aluiziotomazelli/smart-farm-water-tank/logger/raw-logs/field_test_logs_20260715_101221.txt

[2026-07-15 10:12:26.573] [192.168.1.64] I (2303673) UsSensor: 54.6-0, 54.3-0, 54.6-0, 54.7-0, 55.4-0, 54.5-0, 65.0-0
[2026-07-15 10:12:26.601] [192.168.1.64] I (2303693) WaterTankApp: Distance: 54.7 - UsResult 0 | Battery: 3810
[2026-07-15 10:12:32.692] [192.168.1.64] I (2309793) UsSensor: 55.1-0, 59.8-0, 54.5-0, 55.9-0, 64.0-0, 55.9-0, 54.7-0
[2026-07-15 10:12:32.729] [192.168.1.64] I (2309813) WaterTankApp: Distance: 55.2 - UsResult 0 | Battery: 3810
[2026-07-15 10:12:38.813] [192.168.1.64] I (2315913) UsSensor: 54.1-0, 56.1-0, 53.7-0, 54.2-0, 53.7-0, 53.7-0, 54.5-0
[2026-07-15 10:12:38.841] [192.168.1.64] I (2315933) WaterTankApp: Distance: 54.3 - UsResult 0 | Battery: 3810
[2026-07-15 10:12:44.934] [192.168.1.64] I (2322033) UsSensor: 55.1-0, 53.7-0, 54.5-0, 64.4-0, 53.4-0, 57.3-0, 53.7-0
[2026-07-15 10:12:44.963] [192.168.1.64] I (2322053) WaterTankApp: Distance: 54.6 - UsResult 0 | Battery: 3810
[2026-07-15 10:12:51.062] [192.168.1.64] I (2328153) UsSensor: 54.6-0, 65.4-0, 54.2-0, 54.5-0, 54.0-0, 54.0-0, 55.6-0
[2026-07-15 10:12:51.082] [192.168.1.64] I (2328173) WaterTankApp: Distance: 54.5 - UsResult 0 | Battery: 3810
[2026-07-15 10:12:57.176] [192.168.1.64] I (2334273) UsSensor: 54.6-0, 54.7-0, 54.2-0, 53.2-0, 54.0-0, 54.2-0, 63.4-0
[2026-07-15 10:12:57.203] [192.168.1.64] I (2334293) WaterTankApp: Distance: 54.2 - UsResult 0 | Battery: 3810
[2026-07-15 10:13:03.296] [192.168.1.64] I (2340393) UsSensor: 53.3-0, 53.4-0, 53.7-0, 54.2-0, 66.5-0, 57.9-0, 54.0-0
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
[2026-07-15 11:41:11.873] [192.168.1.64] I (7628993) UsSensor: 37.0-0, 39.0-0, 36.7-0, 37.1-0, 37.1-0, 37.0-0, 36.4-0
[2026-07-15 11:41:11.908] [192.168.1.64] I (7629013) WaterTankApp: Distance: 37.2 - UsResult 0 | Battery: 3806
[2026-07-15 11:41:17.993] [192.168.1.64] I (7635113) UsSensor: 36.0-0, 36.1-0, 37.1-0, 38.0-0, 36.7-0, 36.7-0, 37.1-0
[2026-07-15 11:41:18.021] [192.168.1.64] I (7635133) WaterTankApp: Distance: 36.8 - UsResult 0 | Battery: 3806
[2026-07-15 11:41:24.118] [192.168.1.64] I (7641233) UsSensor: 36.0-0, 36.1-0, 36.8-0, 37.1-0, 36.1-0, 36.1-0, 36.1-0
[2026-07-15 11:41:24.141] [192.168.1.64] I (7641253) WaterTankApp: Distance: 36.3 - UsResult 0 | Battery: 3806
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
