aluiziotomazelli/smart-farm-water-tank/docs/water-tank.kicad_sch

## KiCad design docs/water-tank.kicad_sch (2026-08-27)

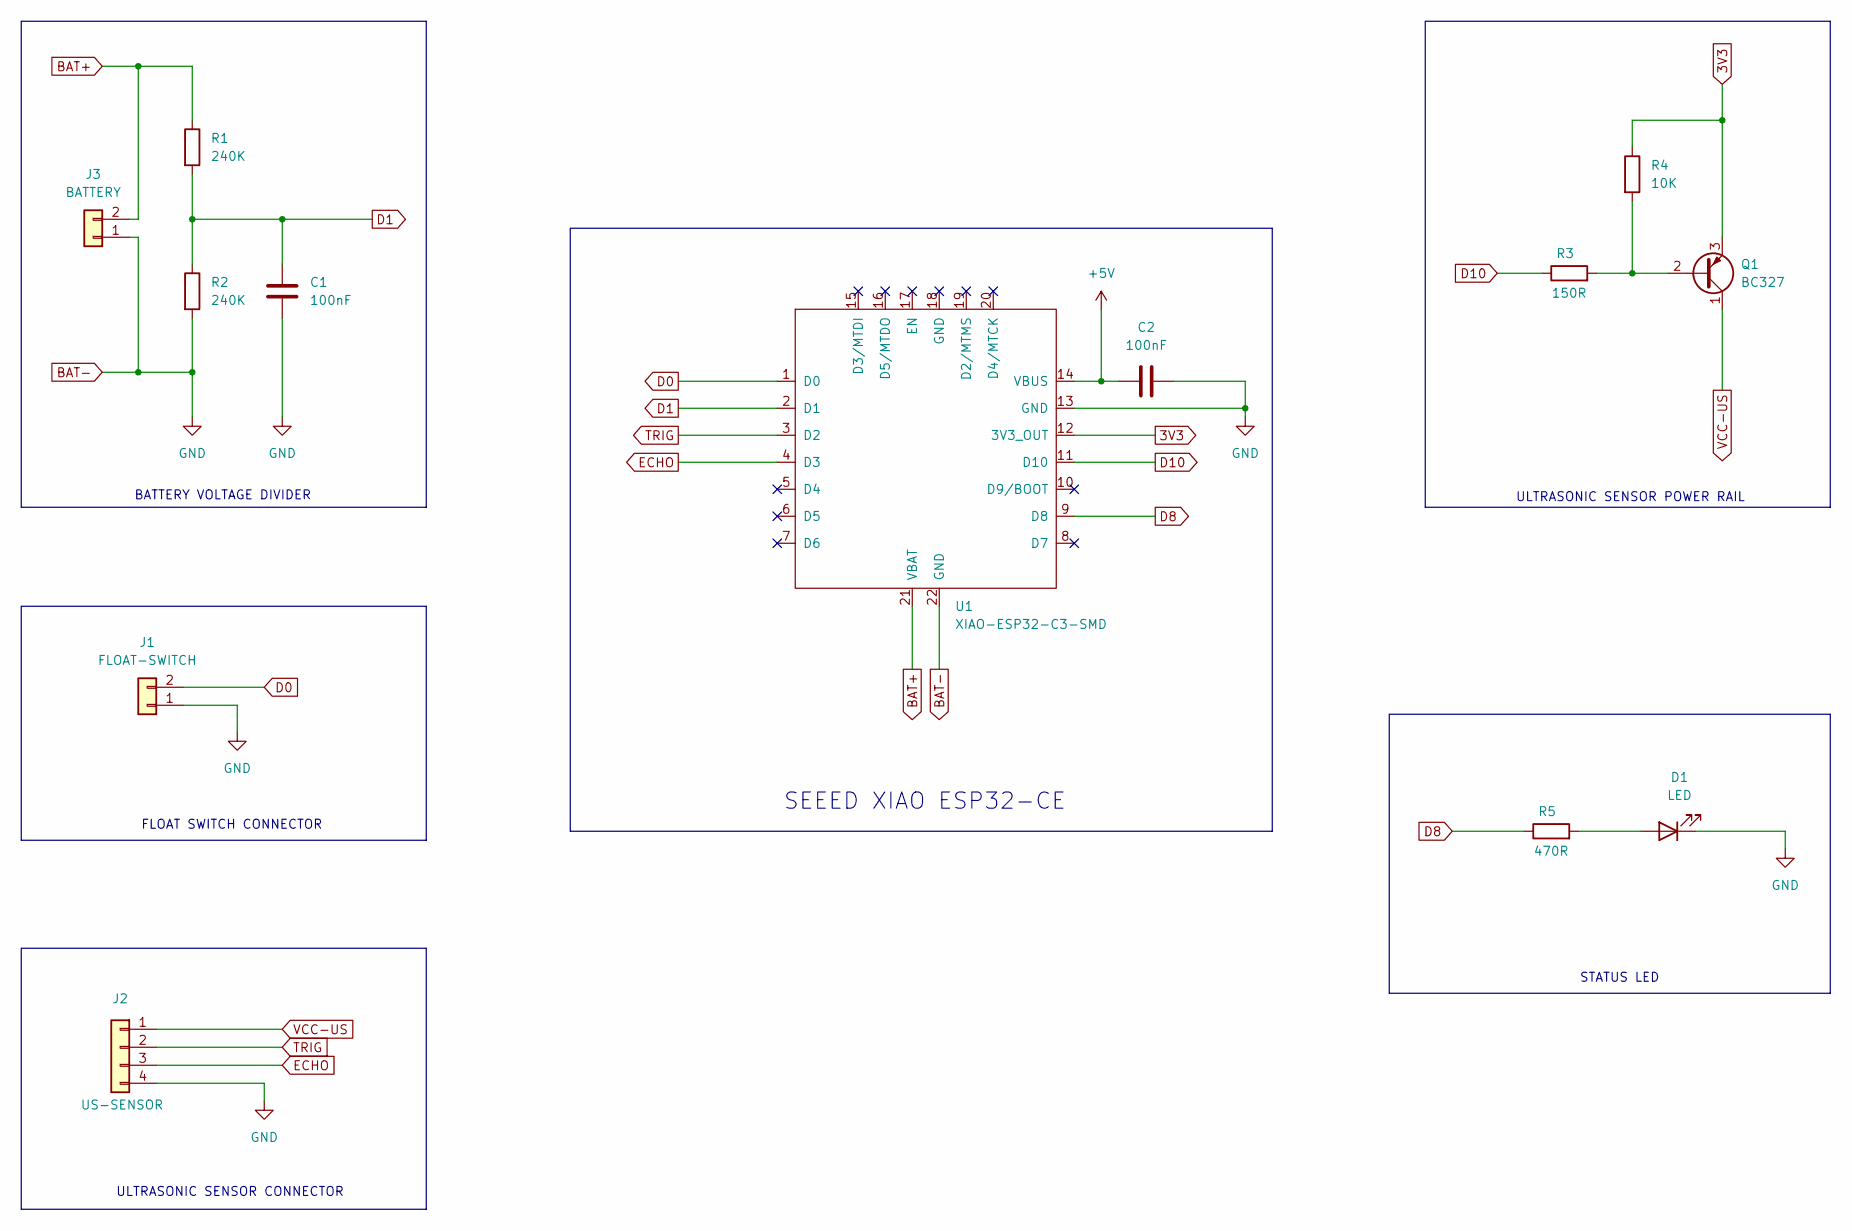
[picture p2: schematic water-tank.kicad_sch]

Parts:
C1, C2: 100nF; C_Disc_D5.0mm_W2.5mm_P5.00mm
D1: LED; LED_D5.0mm
J1: FLOAT-SWITCH; JST_EH_B2B-EH-A_1x02_P2.50mm_Vertical
J2: US-SENSOR; JST_EH_B4B-EH-A_1x04_P2.50mm_Vertical
J3: BATTERY; JST_EH_B2B-EH-A_1x02_P2.50mm_Vertical
Q1: BC327; TO-92L_Inline_Wide
R1, R2: 240K; R_Axial_DIN0207_L6.3mm_D2.5mm_P10.16mm_Horizontal
R3: 150R; R_Axial_DIN0207_L6.3mm_D2.5mm_P10.16mm_Horizontal
R4: 10K; R_Axial_DIN0207_L6.3mm_D2.5mm_P10.16mm_Horizontal
R5: 470R; R_Axial_DIN0207_L6.3mm_D2.5mm_P10.16mm_Horizontal
U1: XIAO-ESP32-C3-SMD; XIAO-ESP32-C3-DIP-SMD

Connections:
3V3: Q1.3 (E), R4.1, U1.12 (3V3_OUT)
+5V: C2.1, U1.14 (VBUS)
BAT+: J3.2, R1.1, U1.21 (VBAT)
BAT-: C1.2, C2.2, D1.1 (K), J1.1, J2.4, J3.1, R2.2, U1.13 (GND), U1.22 (GND)
D0: J1.2, U1.1 (D0)
D1: C1.1, R1.2, R2.1, U1.2 (D1)
D8: R5.1, U1.9 (D8)
D10: R3.1, U1.11 (D10)
ECHO: J2.3, U1.4 (D3)
unnamed: D1.2 (A), R5.2
unnamed: Q1.2 (B), R3.2, R4.2
TRIG: J2.2, U1.3 (D2)
VCC-US: J2.1, Q1.1 (C)

Notes on the sheet:
BATTERY VOLTAGE DIVIDER
SEEED XIAO ESP32-CE
ULTRASONIC SENSOR POWER RAIL
STATUS LED
ULTRASONIC SENSOR CONNECTOR
FLOAT SWITCH CONNECTOR
