aluiziotomazelli/smart-farm-water-tank/main/src/water_tank_logic.cpp

#include "water_tank_logic.hpp"
#include "esp_log.h"

static const char* TAG = "WaterTankLogic";

WaterTankLogic::WaterTankLogic(const TankGeometry& geometry, floatswitch::IFloatSwitch& float_switch)
    : geometry_(geometry)
    , float_switch_(float_switch)
{
}

void WaterTankLogic::process_reading(const ultrasonic::Reading& reading, WaterTankStats& stats)
{
    stats.last_result = reading.result;
    stats.measure_count++;

    update_results_counters(reading.result, stats);

    if (ultrasonic::is_success(reading.result)) {
        stats.last_distance_cm = reading.cm;
        stats.level_permille = geometry_.calculate_permille(reading.cm);
        update_fill_state(stats.level_permille, stats);
        stats.last_level_permille = stats.level_permille; // Store for next iteration
    }
}

void WaterTankLogic::update_operation_mode(WaterTankStats& stats) const
{
    // Update failure counter using a leaky integrator (hysteresis)
    if (!ultrasonic::is_success(stats.last_result)) {
        if (stats.consecutive_failures < CONSECUTIVE_FAILURES_THRESHOLD) {
            stats.consecutive_failures++;
        }
    }
    else if (stats.last_result == ultrasonic::UsResult::OK) {
        if (stats.consecutive_failures > 0) {
            stats.consecutive_failures--;
        }
    }

    // Evaluate backup mode with hysteresis:
    // - Enter backup mode on reaching CONSECUTIVE_FAILURES_THRESHOLD (5 consecutive failures)
    // - Exit backup mode on reaching BACKUP_EXIT_THRESHOLD (requires 2 consecutive OK readings)
    // - Value between BACKUP_EXIT_THRESHOLD and CONSECUTIVE_FAILURES_THRESHOLD is a deadband preserving current state
    constexpr uint8_t BACKUP_EXIT_THRESHOLD = CONSECUTIVE_FAILURES_THRESHOLD - 2; // = 3

    if (stats.consecutive_failures >= CONSECUTIVE_FAILURES_THRESHOLD) {
        stats.backup_mode_active = true;
    }
    else if (stats.consecutive_failures <= BACKUP_EXIT_THRESHOLD) {
        stats.backup_mode_active = false;
    }
}

uint64_t WaterTankLogic::calculate_sleep_time_us(const WaterTankStats& stats, bool is_night) const
{
    if (stats.backup_mode_active) {
        if (!float_switch_.is_tank_full()) {
            return BACKUP_MODE_SLEEP_US;
        }
        else {
            return is_night ? TIMER_STABLE_NIGHT_US : TIMER_STABLE_US;
        }
    }

    uint64_t timer_us = 0;
    if (ultrasonic::is_success(stats.last_result)) {
        switch (stats.fill_state) {
        case FillState::FILLING:
            timer_us = TIMER_FILLING_US;
            break;
        case FillState::DRAINING:
            timer_us = TIMER_DRAIN_US;
            break;
        case FillState::STABLE:
            timer_us = is_night ? TIMER_STABLE_NIGHT_US : TIMER_STABLE_US;
            break;
        default:
            timer_us = TIMER_UNKNOWN_US;
            break;
        }

        if (stats.last_result == ultrasonic::UsResult::WEAK_SIGNAL) {
            timer_us *= WEAK_SLEEP_FACTOR;
        }
    }
    else {
        timer_us = TIMER_UNKNOWN_US * INVALID_SLEEP_FACTOR;
    }

    return timer_us;
}

// =====================================================================
// PRIVATE METHODS
// =====================================================================

void WaterTankLogic::update_fill_state(uint16_t current_permille, WaterTankStats& stats) const
{
    if (stats.last_level_permille == 0) {
        stats.fill_state = FillState::STABLE;
        stats.pending_fill_state = FillState::UNKNOWN;
        stats.pending_state_count = 0;
        return;
    }

    int32_t delta = static_cast<int32_t>(current_permille) - static_cast<int32_t>(stats.last_level_permille);
    uint32_t abs_delta = (delta < 0) ? -delta : delta;

    FillState raw_direction;
    if (abs_delta < LEVEL_DELTA_MIN) {
        raw_direction = FillState::STABLE;
    }
    else if (delta > 0) {
        raw_direction = FillState::FILLING;
    }
    else {
        raw_direction = FillState::DRAINING;
    }

    if (stats.fill_state == FillState::UNKNOWN) {
        stats.fill_state = raw_direction;
        stats.pending_fill_state = FillState::UNKNOWN;
        stats.pending_state_count = 0;
        return;
    }

    if (raw_direction == stats.fill_state) {
        stats.pending_fill_state = FillState::UNKNOWN;
        stats.pending_state_count = 0;
        return;
    }

    if (raw_direction == stats.pending_fill_state) {
        stats.pending_state_count++;
        if (stats.pending_state_count >= FILL_STATE_CONFIRMATIONS_REQUIRED) {
            stats.fill_state = raw_direction;
            stats.pending_fill_state = FillState::UNKNOWN;
            stats.pending_state_count = 0;
            ESP_LOGI(TAG, "FillState transitioned to %d after confirmation", static_cast<int>(raw_direction));
        }
    }
    else {
        stats.pending_fill_state = raw_direction;
        stats.pending_state_count = 1;
    }
}

void WaterTankLogic::update_results_counters(ultrasonic::UsResult result, WaterTankStats& stats)
{
    switch (result) {
    case ultrasonic::UsResult::OK:
        stats.ok_count++;
        break;
    case ultrasonic::UsResult::WEAK_SIGNAL:
        stats.weak_count++;
        break;
    case ultrasonic::UsResult::TIMEOUT:
        stats.timeout_count++;
        break;
    case ultrasonic::UsResult::OUT_OF_RANGE:
        stats.out_of_range_count++;
        break;
    case ultrasonic::UsResult::HIGH_VARIANCE:
        stats.high_variance_count++;
        break;
    case ultrasonic::UsResult::INSUFFICIENT_SAMPLES:
        stats.insufficient_samples_count++;
        break;
    case ultrasonic::UsResult::ECHO_STUCK:
        stats.echo_stuck_count++;
        break;
    case ultrasonic::UsResult::HW_FAULT:
        stats.hw_fault_count++;
        break;
    }
}
